codebehardman/Laser_morse_code/Laser_Transceiver_Schematic.kicad_sch

## KiCad design Laser_Transceiver_Schematic.kicad_sch (2026-10-03)

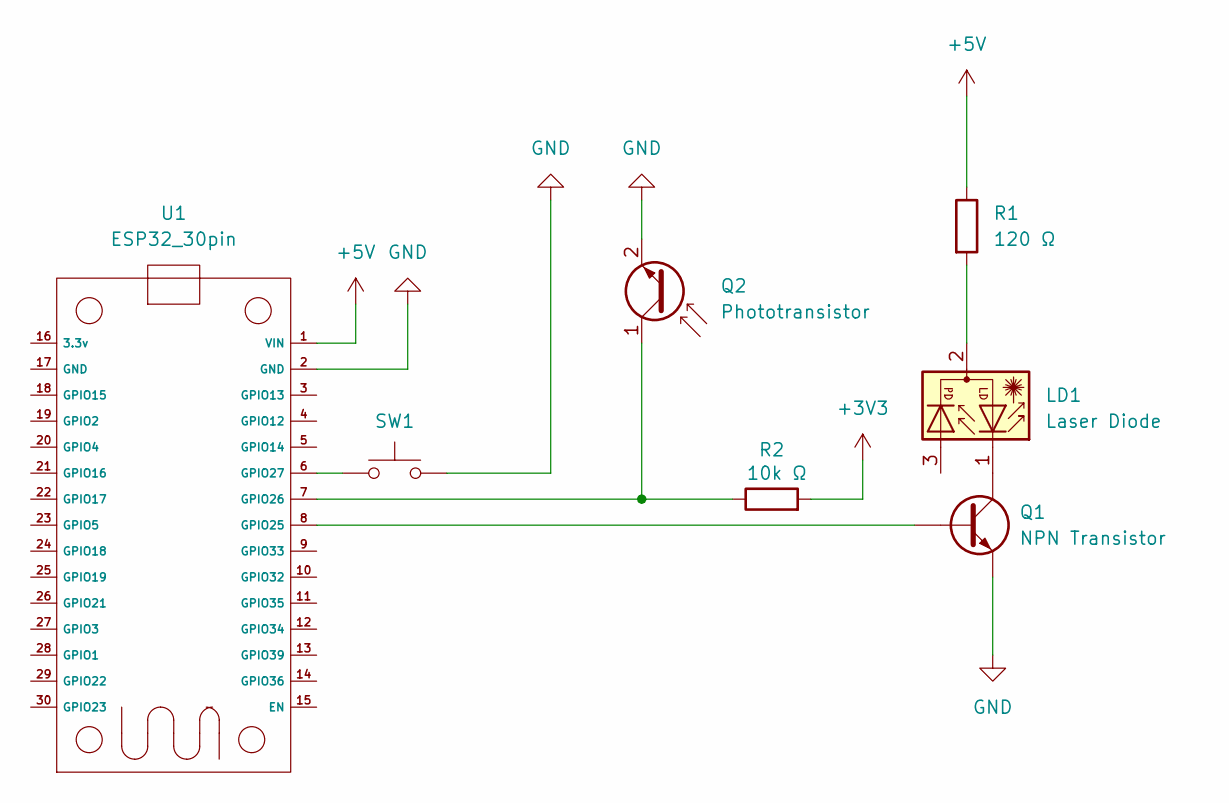
[picture p4: schematic Laser_Transceiver_Schematic.kicad_sch]

Parts:
LD1: Laser Diode; LaserDiode_TO56-3
Q1: NPN Transistor
Q2: Phototransistor; LED_D5.0mm_Clear
R1: 120 Ω
R2: 10k Ω; DIP-8_W7.62mm
SW1: (no value)
U1: ESP32_30pin

Connections:
+3V3: R2.2
+5V: R1.1, U1.1 (VIN)
GND: Q1.E, Q2.2 (E), SW1.2, U1.2 (GND)
unnamed: LD1.1, Q1.C
unnamed: LD1.2, R1.2
unnamed: Q1.B, U1.8 (GPIO25)
unnamed: Q2.1 (C), R2.1, U1.7 (GPIO26)
unnamed: SW1.1, U1.6 (GPIO27)
