codebehardman/Laser_morse_code/src/diagnostics.cpp

#include "diagnostics.hpp"

#include "board_config.hpp"
#include "console.hpp"

namespace diagnostics {
namespace {

// Wait while keeping the inputs sampled.
void waitMs(Device& device, uint32_t durationMs) {
    const uint32_t start = millis();
    while (millis() - start < durationMs) device.updateInputs();
}

// Mirror the receiver on the status LED.
void followSensor(Device& device) { device.led.set(device.sensor.lightDetected()); }

}  // namespace

bool testLaser(Device& device, uint32_t blinks) {
    console::printf("[laser] Blinking %lu times (250 ms on / 250 ms off). Watch the laser.\n",
                    static_cast<unsigned long>(blinks));
    device.sensor.resetActivations();
    for (uint32_t i = 0; i < blinks; ++i) {
        device.laser.set(true);
        waitMs(device, 250);
        device.laser.set(false);
        waitMs(device, 250);
    }
    const uint32_t seen = device.sensor.activations();
    console::printf("[laser] Done. Own phototransistor saw %lu/%lu pulses ",
                    static_cast<unsigned long>(seen), static_cast<unsigned long>(blinks));
    console::println("(0 is normal unless a mirror reflects the beam back).");
    return true;
}

bool testSensor(Device& device, uint32_t durationMs) {
    console::printf("[sensor] Watching phototransistor for %lu s. Shine a laser on it.\n",
                    static_cast<unsigned long>(durationMs / 1000));
    console::printf("[sensor] Current state: %s (level %u, threshold %u)\n",
                    device.sensor.lightDetected() ? "LIGHT" : "dark", device.sensor.readLevel(),
                    device.sensor.threshold());

    device.sensor.resetActivations();
    const uint32_t start = millis();
    uint32_t lastEdge = start;
    while (millis() - start < durationMs) {
        const uint32_t now = millis();
        if (device.sensor.update(now)) {
            console::printf("[sensor] %6lu ms: %s level %4u (previous state lasted %lu ms)\n",
                            static_cast<unsigned long>(now - start),
                            device.sensor.lightDetected() ? "LIGHT" : "dark ",
                            device.sensor.readLevel(), static_cast<unsigned long>(now - lastEdge));
            lastEdge = now;
        }
        followSensor(device);
    }
    device.led.set(false);

    const uint32_t pulses = device.sensor.activations();
    console::printf("[sensor] Done: %lu light pulses detected.\n",
                    static_cast<unsigned long>(pulses));
    if (pulses == 0) {
        console::println("[sensor] FAIL? Nothing seen - check aim, wiring and pull-up.");
        return false;
    }
    return true;
}

void showLevel(Device& device, uint32_t durationMs) {
    constexpr uint32_t kBarWidth = 32;
    console::printf("[level] 0 = bright ... 4095 = dark. Below %u counts as laser.\n",
                    device.sensor.threshold());
    const uint32_t start = millis();
    while (millis() - start < durationMs) {
        const uint16_t level = device.sensor.readLevel();
        char bar[kBarWidth + 1];
        const uint32_t filled = (static_cast<uint32_t>(level) * kBarWidth) / PhotoSensor::kMaxLevel;
        for (uint32_t i = 0; i < kBarWidth; ++i) bar[i] = i < filled ? '#' : '.';
        bar[kBarWidth] = '\0';
        console::printf("[level] %4u |%s| %s\n", level, bar,
                        device.sensor.isLight(level) ? "LASER" : "dark");
        delay(250);
    }
}

namespace {

// Lowest (brightest) level seen during `durationMs`.
uint16_t minimumLevel(Device& device, uint32_t durationMs) {
    uint16_t minimum = PhotoSensor::kMaxLevel;
    const uint32_t start = millis();
    while (millis() - start < durationMs) {
        const uint16_t level = device.sensor.readLevel();
        if (level < minimum) minimum = level;
        delay(2);
    }
    return minimum;
}

}  // namespace

bool calibrateThreshold(Device& device) {
    constexpr uint16_t kMinDifference = 200;

    console::println("[threshold] Step 1/2: measuring the room for 2 s - keep the other laser OFF.");
    delay(500);
    const uint16_t room = minimumLevel(device, 2000);
    console::printf("[threshold] Room level: %u\n", room);

    console::println("[threshold] Step 2/2: hold the OTHER unit's button now so its laser hits this "
                     "sensor (measuring for 5 s)...");
    const uint16_t laser = minimumLevel(device, 5000);
    console::printf("[threshold] Laser level: %u\n", laser);

    if (laser + kMinDifference > room) {
        console::printf("[threshold] FAIL: the laser didn't read clearly brighter than the room. "
                        "Threshold left at %u. Check the aim and try again.\n",
                        device.sensor.threshold());
        return false;
    }
    device.sensor.setThreshold(static_cast<uint16_t>((room + laser) / 2));
    console::printf("[threshold] Threshold set to %u (halfway between room and laser).\n",
                    device.sensor.threshold());
    console::println("[threshold] This lasts until reset. To keep it, put it in "
                     "include/board_config.hpp (kThresholdDarkRoom / kThresholdBrightRoom).");
    return true;
}

bool testButton(Device& device, uint32_t durationMs) {
    console::printf("[button] Press the key a few times within %lu s.\n",
                    static_cast<unsigned long>(durationMs / 1000));
    device.button.resetActivations();
    const uint32_t start = millis();
    while (millis() - start < durationMs) {
        if (device.button.update(millis())) {
            console::println(device.button.pressed() ? "[button] pressed" : "[button] released");
        }
    }
    const uint32_t presses = device.button.activations();
    console::printf("[button] Done: %lu presses.\n", static_cast<unsigned long>(presses));
    return presses > 0;
}

void sendPulses(Device& device, uint32_t count, uint32_t widthMs) {
    console::printf("[link] Sending %lu pulses of %lu ms...\n", static_cast<unsigned long>(count),
                    static_cast<unsigned long>(widthMs));
    device.laser.set(false);
    delay(300);
    for (uint32_t i = 0; i < count; ++i) {
        device.laser.set(true);
        delay(widthMs);
        device.laser.set(false);
        delay(widthMs);
    }
    console::println("[link] Sent.");
}

bool measureEdges(Device& device, uint32_t timeoutMs) {
    constexpr uint32_t kQuietEndUs = 300000;  // stop after this long without a change
    constexpr uint32_t kSentWidthUs = 1000;   // "/test tx 200 1" sends 1 ms on / 1 ms off

    console::printf("[edge] Waiting up to %lu s for pulses - now run '/test tx 200 1' on the "
                    "other unit.\n",
                    static_cast<unsigned long>(timeoutMs / 1000));

    const uint32_t startMs = millis();
    while (!device.sensor.readRaw()) {
        if (millis() - startMs >= timeoutMs) {
            console::println("[edge] FAIL: no light seen.");
            return false;
        }
    }

    // Time every light/dark period with micros(). The first period is
    // partial, so it is skipped.
    bool light = true;
    bool first = true;
    uint32_t lastEdgeUs = micros();
    uint32_t samples = 0;
    uint32_t lightCount = 0, darkCount = 0;
    uint64_t lightSum = 0, darkSum = 0;
    uint32_t lightMin = UINT32_MAX, lightMax = 0, darkMin = UINT32_MAX, darkMax = 0;
    const uint32_t sampleStartUs = lastEdgeUs;

    while (micros() - lastEdgeUs < kQuietEndUs) {
        const bool now = device.sensor.readRaw();
        ++samples;
        if (now == light) continue;
        const uint32_t t = micros();
        const uint32_t duration = t - lastEdgeUs;
        if (!first) {
            if (light) {
                ++lightCount;
                lightSum += duration;
                if (duration < lightMin) lightMin = duration;
                if (duration > lightMax) lightMax = duration;
            } else {
                ++darkCount;
                darkSum += duration;
                if (duration < darkMin) darkMin = duration;
                if (duration > darkMax) darkMax = duration;
            }
        }
        first = false;
        light = now;
        lastEdgeUs = t;
    }
    const uint32_t elapsedUs = lastEdgeUs - sampleStartUs;
    const uint32_t sampleUs = samples > 0 ? elapsedUs / samples : 0;

    if (lightCount < 10 || darkCount < 10) {
        console::printf("[edge] FAIL: only %lu light / %lu dark periods measured. The light may be "
                        "stuck on (threshold too high?) or the pulses merged together.\n",
                        static_cast<unsigned long>(lightCount), static_cast<unsigned long>(darkCount));
        console::printf("[edge] Current level %u, threshold %u.\n", device.sensor.readLevel(),
                        device.sensor.threshold());
        return false;
    }

    const uint32_t lightAvg = static_cast<uint32_t>(lightSum / lightCount);
    const uint32_t darkAvg = static_cast<uint32_t>(darkSum / darkCount);
    console::printf("[edge] %lu pulses. Sent: %lu us light / %lu us dark.\n",
                    static_cast<unsigned long>(lightCount), static_cast<unsigned long>(kSentWidthUs),
                    static_cast<unsigned long>(kSentWidthUs));
    console::printf("[edge] Received light: avg %lu us (min %lu, max %lu)\n",
                    static_cast<unsigned long>(lightAvg), static_cast<unsigned long>(lightMin),
                    static_cast<unsigned long>(lightMax));
    console::printf("[edge] Received dark : avg %lu us (min %lu, max %lu)\n",
                    static_cast<unsigned long>(darkAvg), static_cast<unsigned long>(darkMin),
                    static_cast<unsigned long>(darkMax));
    console::printf("[edge] One sensor reading takes ~%lu us.\n", static_cast<unsigned long>(sampleUs));

    // Light periods come out longer than sent by the time the receiver needs
    // to recover; a bit must be several times longer than that.
    const uint32_t stretchUs = lightAvg > darkAvg ? (lightAvg - darkAvg) / 2 : 0;
    const uint32_t jitterUs = (lightMax - lightMin) / 2;
    const uint32_t slowUs = stretchUs + jitterUs + sampleUs;
    const uint32_t bauds[] = {9600, 4800, 2400, 1200, 600, 300};
    uint32_t recommended = 0;
    for (uint32_t baud : bauds) {
        if (1000000 / baud >= 4 * slowUs) {
            recommended = baud;
            break;
        }
    }
    console::printf("[edge] Light pulses are stretched by ~%lu us (jitter +-%lu us).\n",
                    static_cast<unsigned long>(stretchUs), static_cast<unsigned long>(jitterUs));
    if (recommended == 0) {
        console::println("[edge] The receiver is too slow even for 300 baud: use a smaller "
                         "pull-up resistor (and check the threshold).");
        return false;
    }
    console::printf("[edge] Highest safe link speed: %lu baud (use /baud %lu in serial mode on "
                    "both units).\n",
                    static_cast<unsigned long>(recommended), static_cast<unsigned long>(recommended));
    return true;
}

bool countPulses(Device& device, uint32_t expected, uint32_t timeoutMs) {
    constexpr uint32_t kQuietEndMs = 500;  // stop after this long without pulses

    console::printf("[link] Waiting up to %lu s for pulses - now run '/test tx' on the other unit.\n",
                    static_cast<unsigned long>(timeoutMs / 1000));

    uint32_t count = 0;
    uint32_t minWidth = UINT32_MAX;
    uint32_t maxWidth = 0;
    uint32_t riseMs = 0;
    uint32_t lastActivityMs = 0;
    const uint32_t start = millis();

    while (true) {
        const uint32_t now = millis();
        if (device.sensor.update(now)) {
            lastActivityMs = now;
            if (device.sensor.lightDetected()) {
                riseMs = now;
            } else if (riseMs != 0) {
                const uint32_t width = now - riseMs;
                if (width < minWidth) minWidth = width;
                if (width > maxWidth) maxWidth = width;
                ++count;
            }
        }
        if (count == 0 && now - start >= timeoutMs) break;
        if (count > 0 && now - lastActivityMs >= kQuietEndMs) break;
    }

    if (count == 0) {
        console::println("[link] FAIL: no pulses received.");
        return false;
    }

    const uint32_t missing = count >= expected ? 0 : expected - count;
    const uint32_t errorPct = (100 * (count > expected ? count - expected : missing)) / expected;
    console::printf("[link] Received %lu/%lu pulses (error %lu%%), width min %lu ms / max %lu ms.\n",
                    static_cast<unsigned long>(count), static_cast<unsigned long>(expected),
                    static_cast<unsigned long>(errorPct), static_cast<unsigned long>(minWidth),
                    static_cast<unsigned long>(maxWidth));
    const bool pass = errorPct <= 10;  // design requirement: <= 10% error rate
    console::println(pass ? "[link] PASS" : "[link] FAIL: error rate above 10%");
    return pass;
}

}  // namespace diagnostics
