codebehardman/Laser_morse_code/src/drivers/debounced_input.hpp

#pragma once

#include <Arduino.h>

// Input that only changes state after the raw reading has been stable for
// the debounce time. Subclasses can override readRaw() to change how the
// pin is read (e.g. analog with a threshold).
class DebouncedInput {
public:
    DebouncedInput(uint32_t pin, bool activeLow, uint32_t debounceMs, bool usePullup)
        : pin_(pin), activeLow_(activeLow), debounceMs_(debounceMs), usePullup_(usePullup) {}
    virtual ~DebouncedInput() = default;

    void begin();

    // Sample the input. Returns true if the debounced state changed.
    bool update(uint32_t nowMs);

    bool active() const { return state_; }

    // Undebounced reading: true = active.
    virtual bool readRaw() const;

    // Number of inactive -> active transitions since the last reset.
    uint32_t activations() const { return activations_; }
    void resetActivations() { activations_ = 0; }

protected:
    uint32_t pin() const { return pin_; }

private:
    uint32_t pin_;
    bool activeLow_;
    uint32_t debounceMs_;
    bool usePullup_;

    bool state_ = false;
    bool lastRaw_ = false;
    uint32_t lastChangeMs_ = 0;
    uint32_t activations_ = 0;
};
